nager/Nager.ArduinoStepperMotor/src/Arduino/RadiatorControl/RadiatorControl.ino

#include <Wire.h>
#include <SPI.h>
#include <Adafruit_Sensor.h>
#include <Adafruit_BME280.h>

Adafruit_BME280 bme; // I2C

unsigned int loopCounter = 0;
unsigned int loopMessageInterval = 500;

float desiredTemperature = 23;
float currentTemperature = 0;

void setup() {
  //Serial configuration
  Serial.setTimeout(50);
  Serial.begin(115200);

  Serial.println("Start humidity");
  humiditySensorSetup();
  Serial.println("Start motor");
  motorControlSetup();

  //Set limit for the other direction
  unsigned long currentPosition = getCurrentPosition();
  setLimitLeft(currentPosition - 800);
}

void loop() {
  commandProcessing();
  checkEndstops();


  if (loopCounter == loopMessageInterval) {
    currentTemperature = bme.readTemperature();

    //Serial.println(temperature);
    if (currentTemperature < desiredTemperature) {
      //Open radiator
      setMotorSpeed(1);
    } else {
      setMotorSpeed(-1);
    }

    Serial.println((String)"{ \"availableStepsLeft\":" + checkLeftLimit() +  ", \"availableStepsRight\":" + checkRightLimit() + ", \"motorSpeed\":" + getMotorSpeed() + ", \"temp\":" + currentTemperature + " }");
    loopCounter = 0;
  }

  delayMicroseconds(50);
  loopCounter++;
}
